makgyber/kiai-split/images/IMG_8397.jpeg

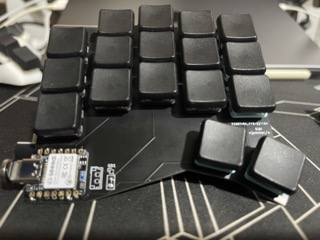
images/IMG_8397.jpeg
